tolgaozuygur/diy_electric_salt_spoon/3d/spoonAssembly.SLDASM

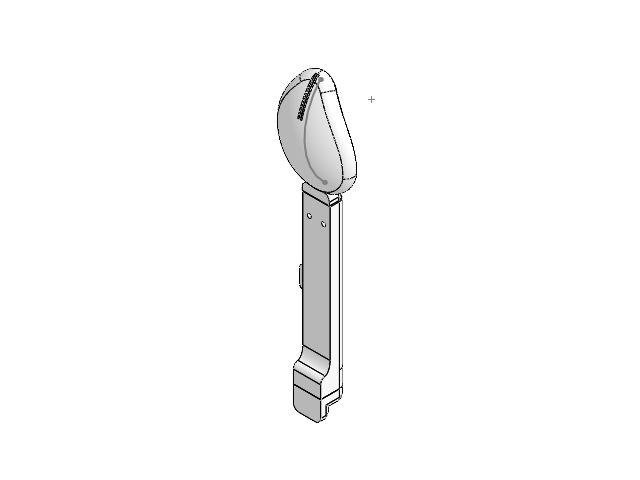
[picture p16: CAD file, 2026-04-08]
3d/spoonAssembly.SLDASM
spoon_middle
spoon_socket_holder
spoon_stripe
spoon_tip
