tolgaozuygur/diy_electric_salt_spoon/electronics/salt_spoon/salt_spoon.kicad_sch

## KiCad design electronics/salt_spoon/salt_spoon.kicad_sch (2026-04-08)

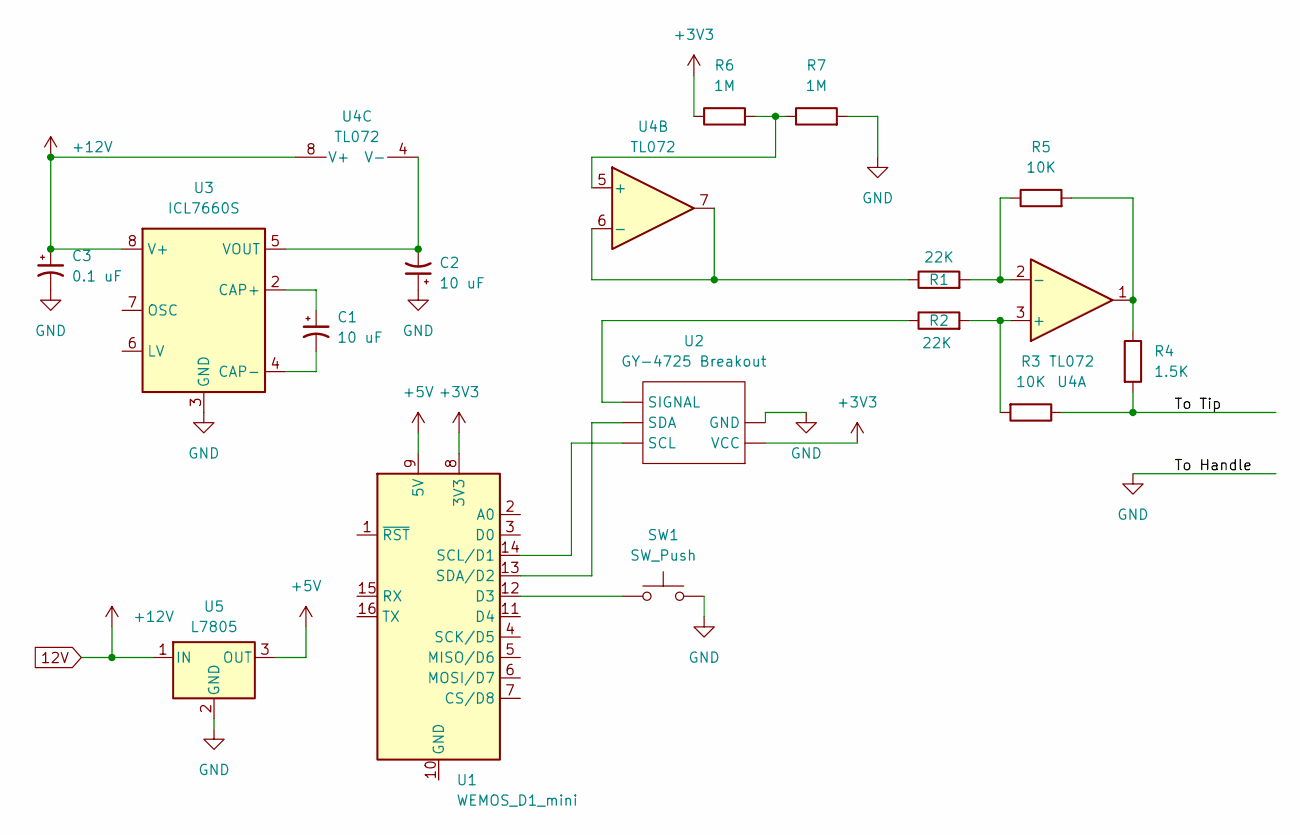
[picture p17: schematic salt_spoon.kicad_sch]

Parts:
C1, C2: 10 uF
C3: 0.1 uF
R1, R2: 22K
R3, R5: 10K
R4: 1.5K
R6, R7: 1M
SW1: SW_Push
U1: WEMOS_D1_mini; WEMOS_D1_mini_light
U2: GY-4725 Breakout
U3: ICL7660S
U4: TL072
U5: L7805

Connections:
+3V3: R6.1, U1.8 (3V3), U2.
+5V: U1.9 (5V), U5.3 (OUT)
+12V: C3.1, U3.8 (V+), U4.8 (V+), U5.1 (IN)
GND: C2.1, C3.2, R7.2, SW1.2, U2., U3.3 (GND), U5.2 (GND)
unnamed: C1.1, U3.2 (CAP+)
unnamed: C1.2, U3.4 (CAP-)
unnamed: C2.2, U3.5 (VOUT), U4.4 (V-)
unnamed: R1.1, U4.6 (-), U4.7
unnamed: R1.2, R5.1, U4.2 (-)
unnamed: R2.1, U2.
unnamed: R2.2, R3.2, U4.3 (+)
unnamed: R4.1, R5.2, U4.1
unnamed: R6.2, R7.1, U4.5 (+)
unnamed: SW1.1, U1.12 (D3)
unnamed: U1.13 (SDA/D2), U2.
unnamed: U1.14 (SCL/D1), U2.
To Tip: R3.1, R4.2
